FREILab/easyVerwaltungHardware/hardware/projects/RFID_BOX/ECAD/RFID_Board/antenna/render_78x78_3T.png

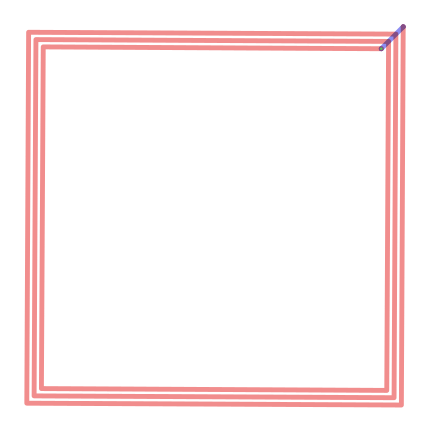
hardware/projects/RFID_BOX/ECAD/RFID_Board/antenna/render_78x78_3T.png
