FREILab/easyVerwaltungHardware/hardware/projects/MicBac/PROJ-FRL-RIFD_Box/Electro/3D/Card 1.stp

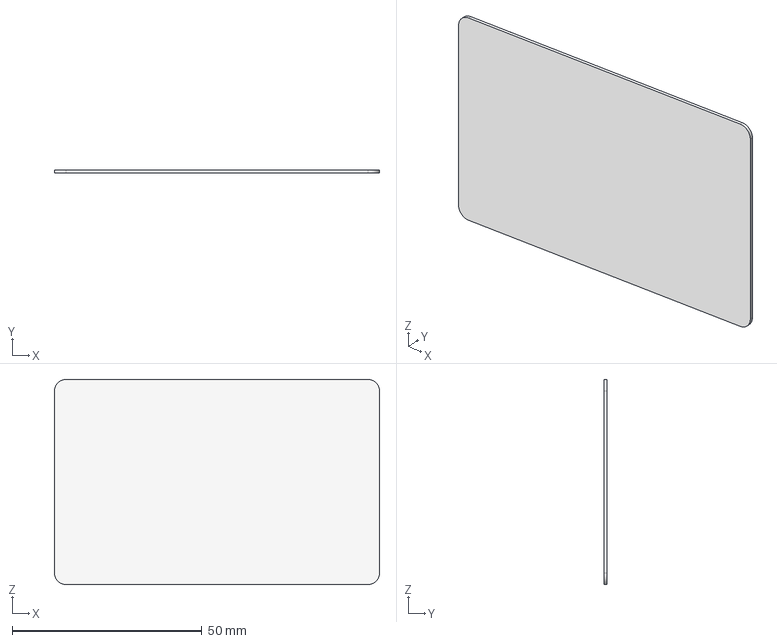
[picture p21: CAD file, 2026-07-29]
hardware/projects/MicBac/PROJ-FRL-RIFD_Box/Electro/3D/Card 1.stp
85.6 x 0.8 x 54.0 mm
