FREILab/easyVerwaltungHardware/hardware/projects/MicBac/PROJ-FRL-RIFD_Box/Mech/CAD/SW/SB-PCB_Enclosure.STEP

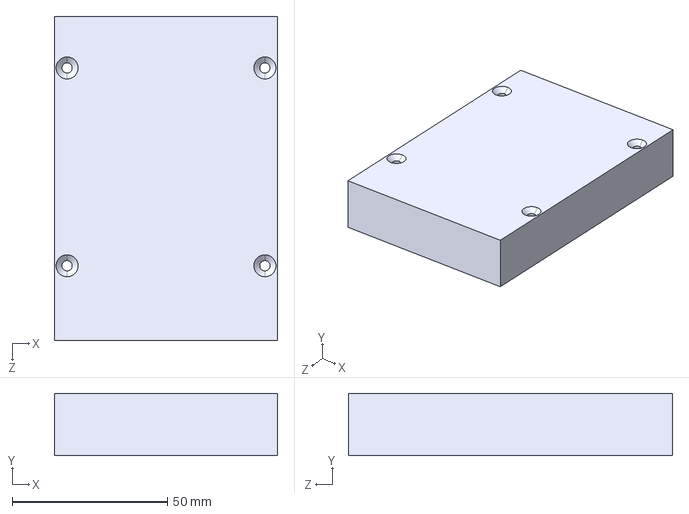
[picture p22: CAD file, 2026-07-29]
hardware/projects/MicBac/PROJ-FRL-RIFD_Box/Mech/CAD/SW/SB-PCB_Enclosure.STEP
72.0 x 20.0 x 104.5 mm
