FREILab/easyVerwaltungHardware/hardware/projects/MicBac/PROJ-FRL-RIFD_Box/Electro/3D/Finder_41.52.STEP

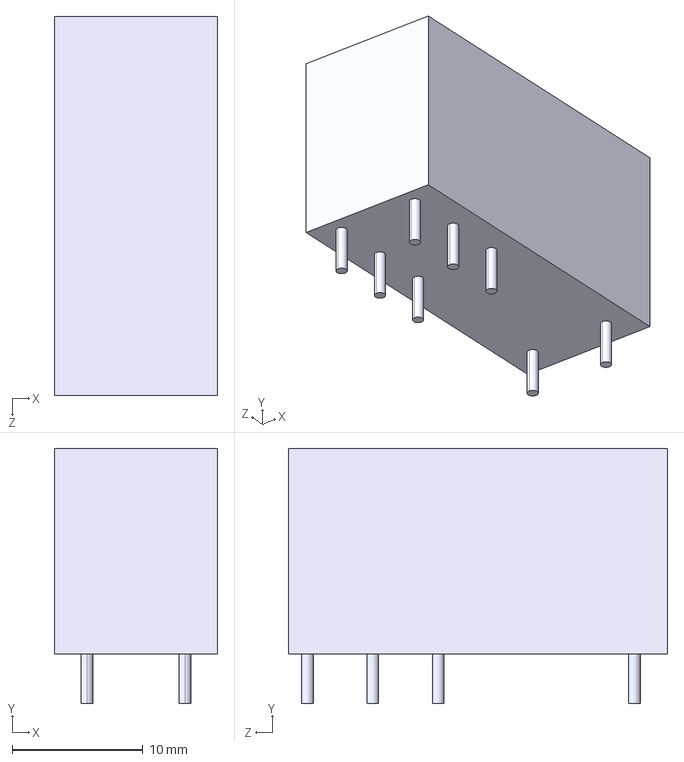
[picture p23: CAD file, 2026-07-29]
hardware/projects/MicBac/PROJ-FRL-RIFD_Box/Electro/3D/Finder_41.52.STEP
12.5 x 19.5 x 29.0 mm
