FREILab/easyVerwaltungHardware/hardware/projects/MicBac/PROJ-FRL-RIFD_Box/PROJ-FL-RFiD_Box_SOLIDWORKS/RFID_Box_Layer_Case.SLDPRT

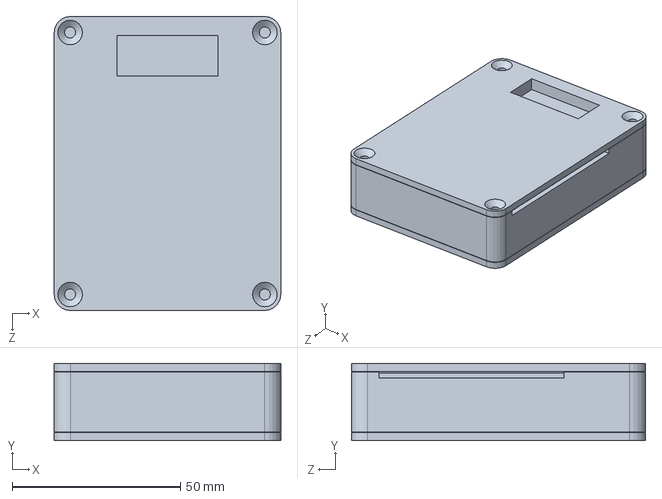
[picture p24: CAD file, 2026-07-29]
hardware/projects/MicBac/PROJ-FRL-RIFD_Box/PROJ-FL-RFiD_Box_SOLIDWORKS/RFID_Box_Layer_Case.SLDPRT
67.3 x 23.0 x 87.3 mm
