FREILab/easyVerwaltungHardware/hardware/projects/MicBac/PROJ-FRL-RIFD_Box/Electro/3D/RAC05-24SK--3DModel-STEP-498702.STEP

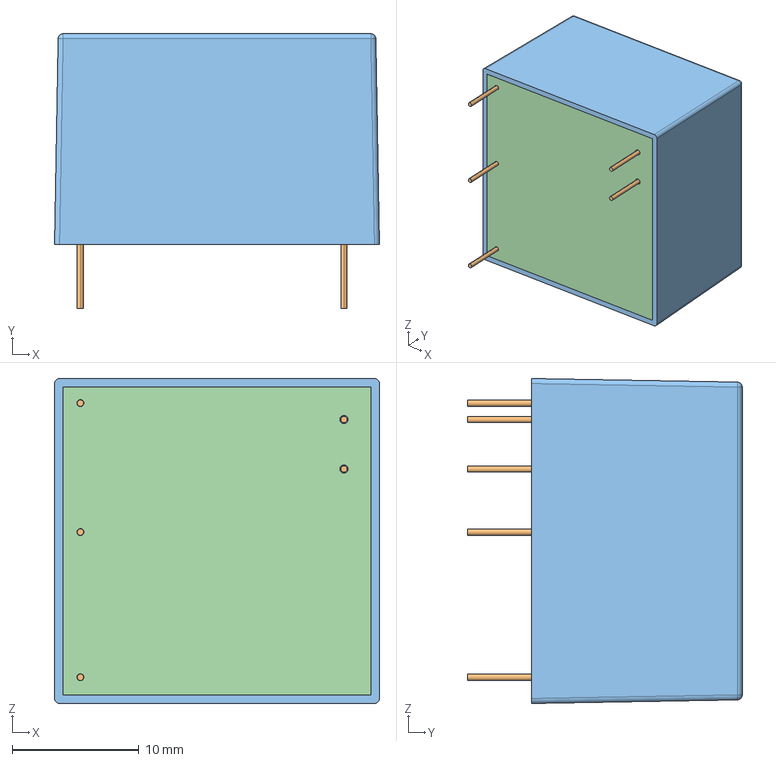
[picture p25: CAD file, 2026-07-29]
hardware/projects/MicBac/PROJ-FRL-RIFD_Box/Electro/3D/RAC05-24SK--3DModel-STEP-498702.STEP
25.6 x 21.6 x 25.6 mm
