FREILab/easyVerwaltungHardware/hardware/projects/MicBac/PROJ-FRL-RIFD_Box/Mech/CAD/SW/SB-Spring.STEP

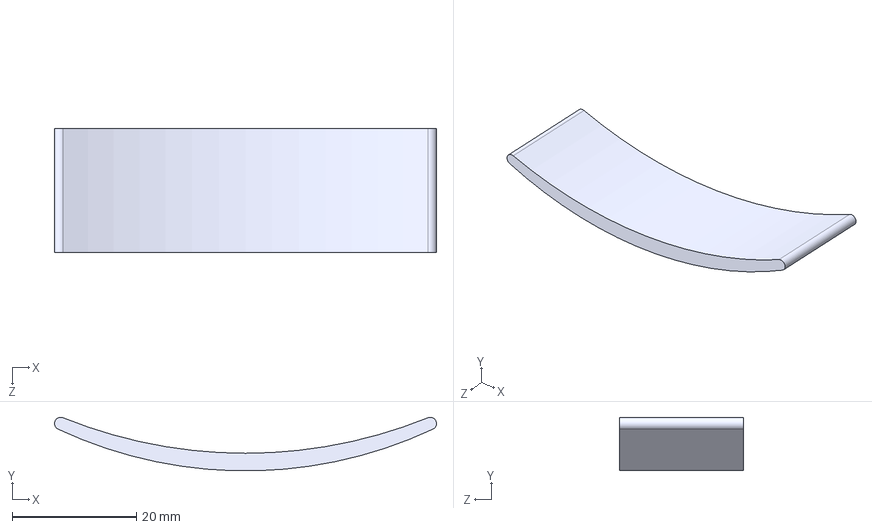
[picture p26: CAD file, 2026-07-29]
hardware/projects/MicBac/PROJ-FRL-RIFD_Box/Mech/CAD/SW/SB-Spring.STEP
61.4 x 8.58 x 20.0 mm
